lucashudson-eng/rover-vacuum-cleaner/rover_vacuum_cleaner/models/rover/meshes/LD14P_Link.STL

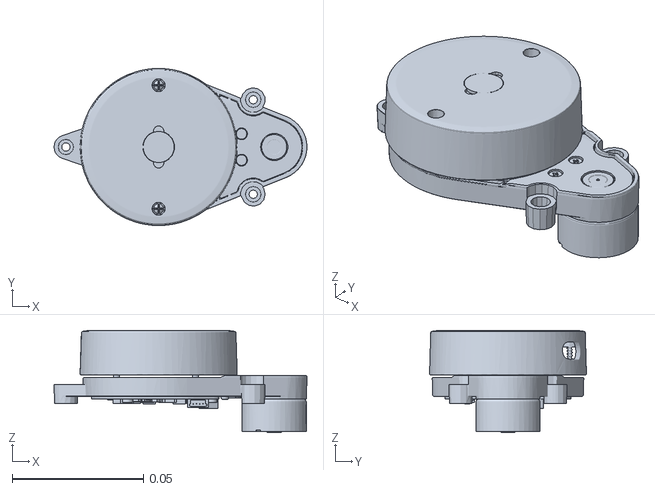
[picture p13: CAD file, 2025-10-14]
rover_vacuum_cleaner/models/rover/meshes/LD14P_Link.STL
0.0963 x 0.0597 x 0.0388
