lucashudson-eng/rover-vacuum-cleaner/codes/ina219/ina219.ino

#include <Wire.h>
#include <Adafruit_INA219.h>

Adafruit_INA219 ina219;


void setup(void) 
{
  Serial.begin(115200);
  
  // Initialize the INA219.
  // By default the initialization will use the largest range (32V, 2A).  However
  // you can call a setCalibration function to change this range (see comments).
  if (! ina219.begin()) {
    Serial.println("Failed to find INA219 chip");
    while (1) { delay(10); }
  }

  Serial.println("Measuring voltage and current with INA219 ...");
}

void loop(void) 
{
  float busvoltage = 0;
  float current_mA = 0;
  float power_mW = 0;

  busvoltage = ina219.getBusVoltage_V();
  current_mA = ina219.getCurrent_mA();
  power_mW = ina219.getPower_mW();
  
  Serial.print("Bus Voltage:   "); Serial.print(busvoltage); Serial.println(" V");
  Serial.print("Current:       "); Serial.print(current_mA); Serial.println(" mA");
  Serial.print("Power:         "); Serial.print(power_mW); Serial.println(" mW");
  Serial.println("");

  delay(2000);
}
